jensws80/JensArduinoCarPedals/pedalElectricalDrawings.sch

## EAGLE design pedalElectricalDrawings.sch (2018-02-18)

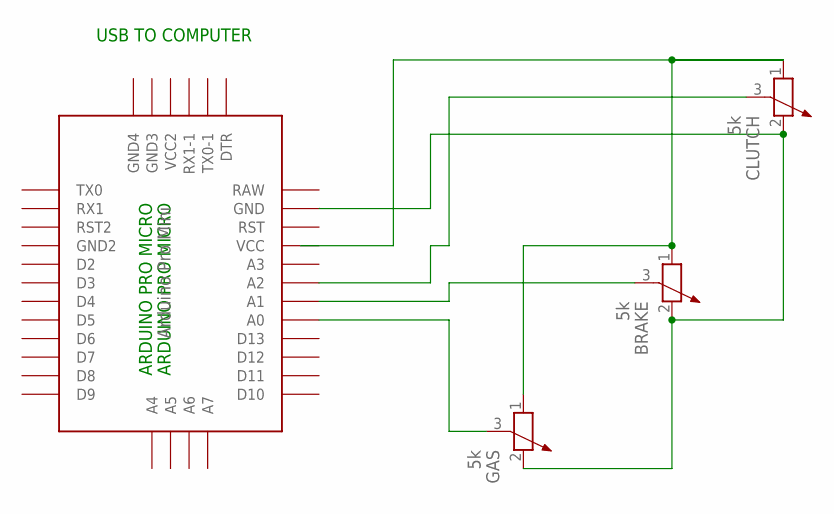
[picture p6: schematic pedalElectricalDrawings.sch]

Parts:
BRAKE: 5k; PT-10
CLUTCH: 5k; PT-10
GAS: 5k; PT-10
U$1: PRO-MINI

Connections:
unnamed: GAS.3, U$1.A0
unnamed: BRAKE.3, U$1.A1
unnamed: CLUTCH.3, U$1.A2
unnamed: BRAKE.2, CLUTCH.2, GAS.2, U$1.GND
unnamed: BRAKE.1, CLUTCH.1, GAS.1

Notes on the sheet:
USB TO COMPUTER
ARDUINO PRO MICRO
